JasonLash/J-Frame/src/cert.h

#ifndef CERT_H_
#define CERT_H_
unsigned char example_crt_DER[] = {
  0x30, 0x82, 0x04, 0x4f, 0x30, 0x82, 0x03, 0x37, 0xa0, 0x03, 0x02, 0x01,
  0x02, 0x02, 0x12, 0x03, 0x94, 0x52, 0x84, 0x9a, 0x21, 0x40, 0xc7, 0xe4,
  0x87, 0x2b, 0x64, 0x8a, 0xef, 0xa2, 0x51, 0x67, 0x66, 0x30, 0x0d, 0x06,
  0x09, 0x2a, 0x86, 0x48, 0x86, 0xf7, 0x0d, 0x01, 0x01, 0x0b, 0x05, 0x00,
  0x30, 0x32, 0x31, 0x0b, 0x30, 0x09, 0x06, 0x03, 0x55, 0x04, 0x06, 0x13,
  0x02, 0x55, 0x53, 0x31, 0x16, 0x30, 0x14, 0x06, 0x03, 0x55, 0x04, 0x0a,
  0x13, 0x0d, 0x4c, 0x65, 0x74, 0x27, 0x73, 0x20, 0x45, 0x6e, 0x63, 0x72,
  0x79, 0x70, 0x74, 0x31, 0x0b, 0x30, 0x09, 0x06, 0x03, 0x55, 0x04, 0x03,
  0x13, 0x02, 0x52, 0x33, 0x30, 0x1e, 0x17, 0x0d, 0x32, 0x33, 0x30, 0x32,
  0x31, 0x33, 0x32, 0x32, 0x32, 0x34, 0x32, 0x33, 0x5a, 0x17, 0x0d, 0x32,
  0x33, 0x30, 0x35, 0x31, 0x34, 0x32, 0x32, 0x32, 0x34, 0x32, 0x32, 0x5a,
  0x30, 0x15, 0x31, 0x13, 0x30, 0x11, 0x06, 0x03, 0x55, 0x04, 0x03, 0x13,
  0x0a, 0x6a, 0x66, 0x72, 0x61, 0x6d, 0x65, 0x2e, 0x63, 0x61, 0x6d, 0x30,
  0x59, 0x30, 0x13, 0x06, 0x07, 0x2a, 0x86, 0x48, 0xce, 0x3d, 0x02, 0x01,
  0x06, 0x08, 0x2a, 0x86, 0x48, 0xce, 0x3d, 0x03, 0x01, 0x07, 0x03, 0x42,
  0x00, 0x04, 0xcc, 0xce, 0xe2, 0x82, 0xc3, 0x87, 0xf6, 0x3d, 0xdb, 0x2e,
  0xff, 0xdb, 0x9c, 0x84, 0xdc, 0x52, 0x1b, 0xb1, 0xd6, 0xc9, 0x75, 0xfe,
  0x54, 0x95, 0xc0, 0x51, 0x3a, 0x86, 0x5c, 0x3e, 0xae, 0xb3, 0x19, 0x95,
  0x43, 0x04, 0x34, 0xde, 0xd7, 0xd3, 0x19, 0xdc, 0xa7, 0xc6, 0x9f, 0xd0,
  0xe3, 0x1b, 0x51, 0x59, 0xd4, 0xb6, 0x55, 0x01, 0xd0, 0xa6, 0xd5, 0x8e,
  0x29, 0xdf, 0x30, 0x45, 0x17, 0xee, 0xa3, 0x82, 0x02, 0x45, 0x30, 0x82,
  0x02, 0x41, 0x30, 0x0e, 0x06, 0x03, 0x55, 0x1d, 0x0f, 0x01, 0x01, 0xff,
  0x04, 0x04, 0x03, 0x02, 0x07, 0x80, 0x30, 0x1d, 0x06, 0x03, 0x55, 0x1d,
  0x25, 0x04, 0x16, 0x30, 0x14, 0x06, 0x08, 0x2b, 0x06, 0x01, 0x05, 0x05,
  0x07, 0x03, 0x01, 0x06, 0x08, 0x2b, 0x06, 0x01, 0x05, 0x05, 0x07, 0x03,
  0x02, 0x30, 0x0c, 0x06, 0x03, 0x55, 0x1d, 0x13, 0x01, 0x01, 0xff, 0x04,
  0x02, 0x30, 0x00, 0x30, 0x1d, 0x06, 0x03, 0x55, 0x1d, 0x0e, 0x04, 0x16,
  0x04, 0x14, 0xf8, 0x14, 0x30, 0xc5, 0xa9, 0x7a, 0x51, 0xaa, 0x60, 0xff,
  0xd2, 0x33, 0xbc, 0x0d, 0x99, 0x77, 0xfc, 0xe3, 0x42, 0x2c, 0x30, 0x1f,
  0x06, 0x03, 0x55, 0x1d, 0x23, 0x04, 0x18, 0x30, 0x16, 0x80, 0x14, 0x14,
  0x2e, 0xb3, 0x17, 0xb7, 0x58, 0x56, 0xcb, 0xae, 0x50, 0x09, 0x40, 0xe6,
  0x1f, 0xaf, 0x9d, 0x8b, 0x14, 0xc2, 0xc6, 0x30, 0x55, 0x06, 0x08, 0x2b,
  0x06, 0x01, 0x05, 0x05, 0x07, 0x01, 0x01, 0x04, 0x49, 0x30, 0x47, 0x30,
  0x21, 0x06, 0x08, 0x2b, 0x06, 0x01, 0x05, 0x05, 0x07, 0x30, 0x01, 0x86,
  0x15, 0x68, 0x74, 0x74, 0x70, 0x3a, 0x2f, 0x2f, 0x72, 0x33, 0x2e, 0x6f,
  0x2e, 0x6c, 0x65, 0x6e, 0x63, 0x72, 0x2e, 0x6f, 0x72, 0x67, 0x30, 0x22,
  0x06, 0x08, 0x2b, 0x06, 0x01, 0x05, 0x05, 0x07, 0x30, 0x02, 0x86, 0x16,
  0x68, 0x74, 0x74, 0x70, 0x3a, 0x2f, 0x2f, 0x72, 0x33, 0x2e, 0x69, 0x2e,
  0x6c, 0x65, 0x6e, 0x63, 0x72, 0x2e, 0x6f, 0x72, 0x67, 0x2f, 0x30, 0x15,
  0x06, 0x03, 0x55, 0x1d, 0x11, 0x04, 0x0e, 0x30, 0x0c, 0x82, 0x0a, 0x6a,
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
};
unsigned int example_crt_DER_len = 1107;
#endif
